defillo/lipo-battery-tester/20200904_072432.jpg

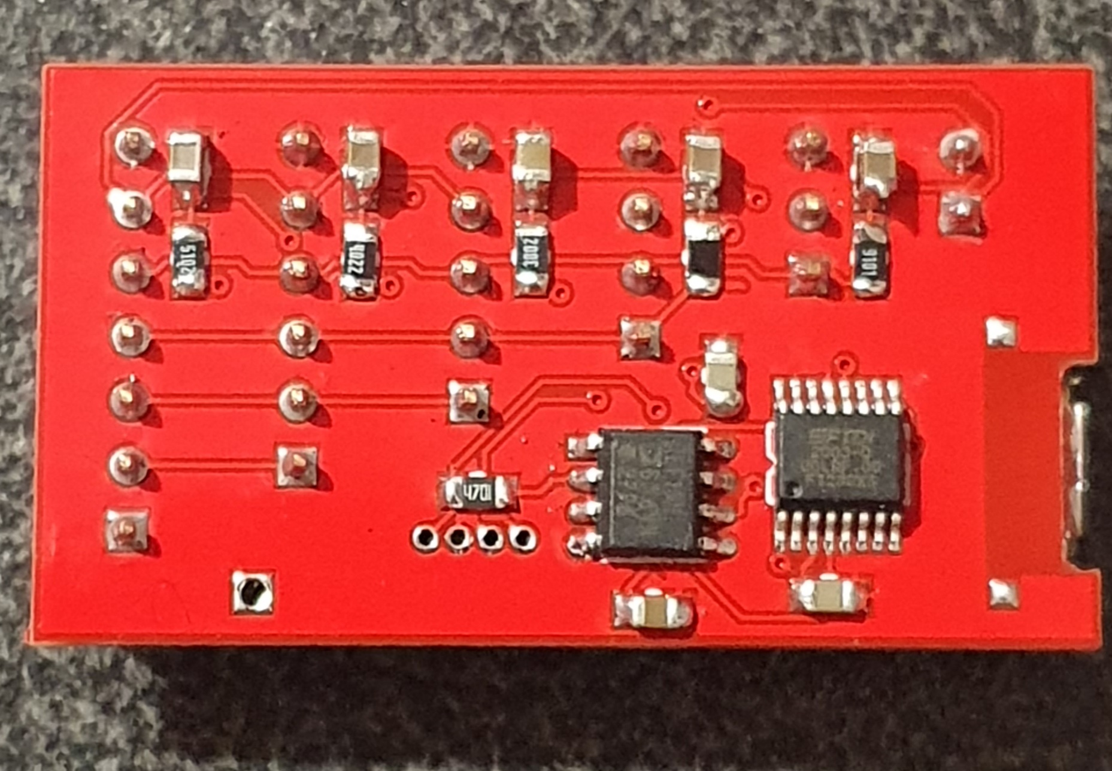
20200904_072432.jpg
